maqy0827/22GD/Book/Image/PCB-已焊接.jpg

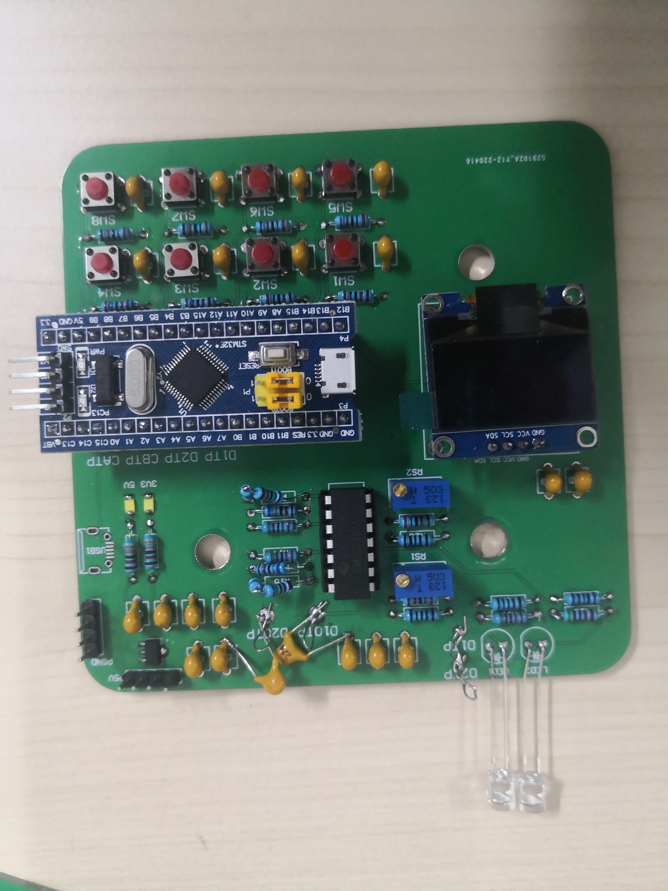
Book/Image/PCB-已焊接.jpg
