maqy0827/22GD/Book/Image/PCB-未焊接.jpg

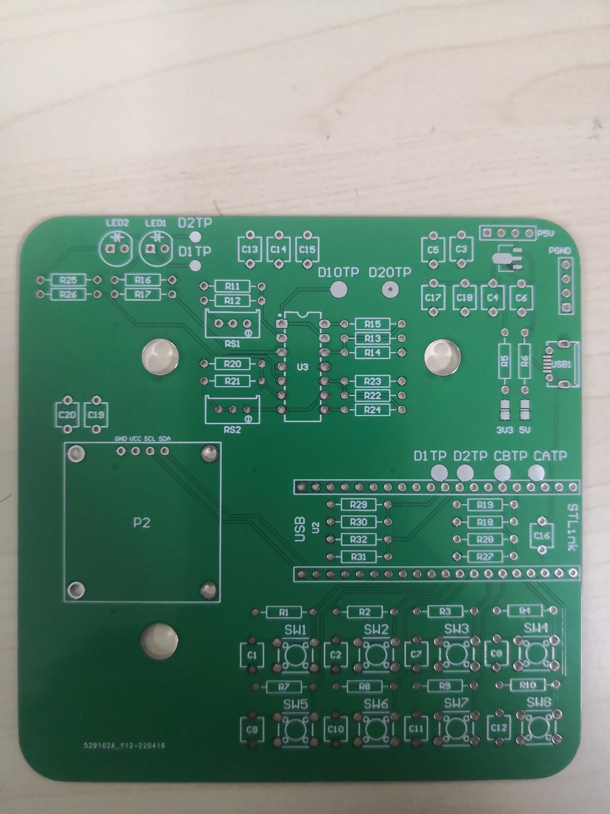
Book/Image/PCB-未焊接.jpg
