maqy0827/22GD/Book/Image/分光片干涉图样.jpg

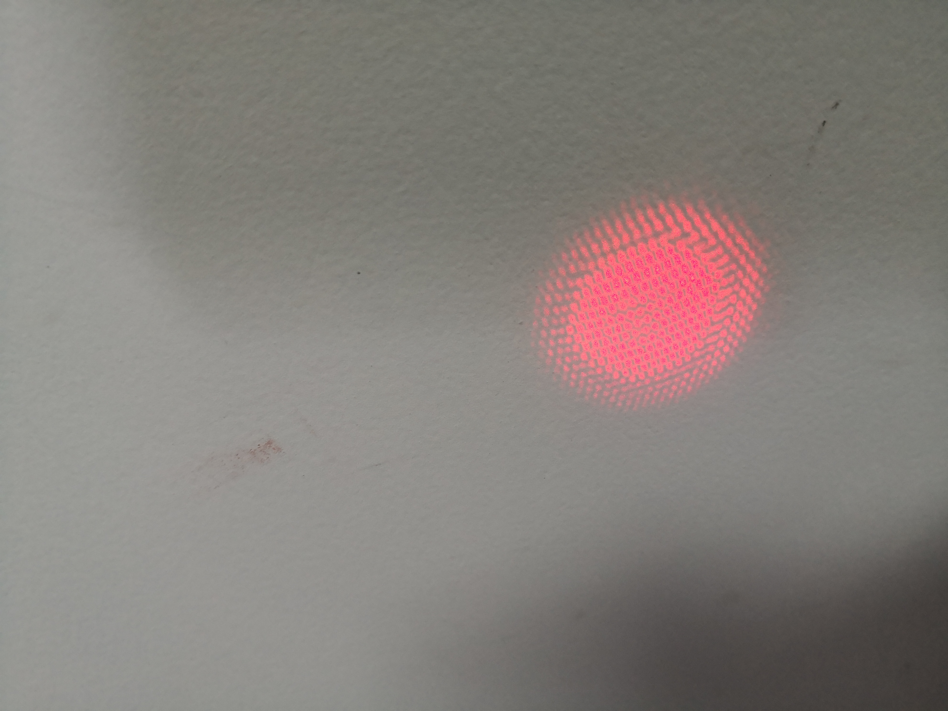
Book/Image/分光片干涉图样.jpg
