maqy0827/22GD/Book/Image/并联101原始信号.jpg

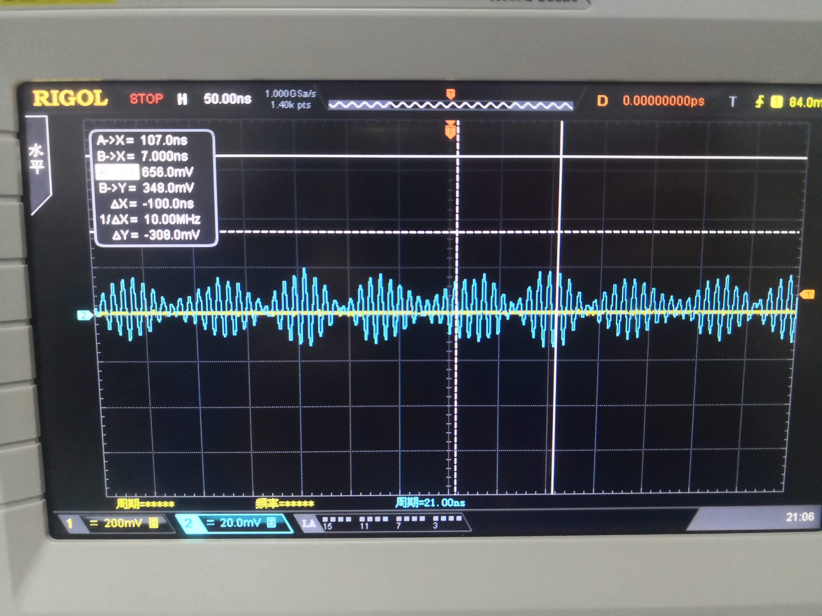
Book/Image/并联101原始信号.jpg
