maqy0827/22GD/Book/Image/放大前.jpg

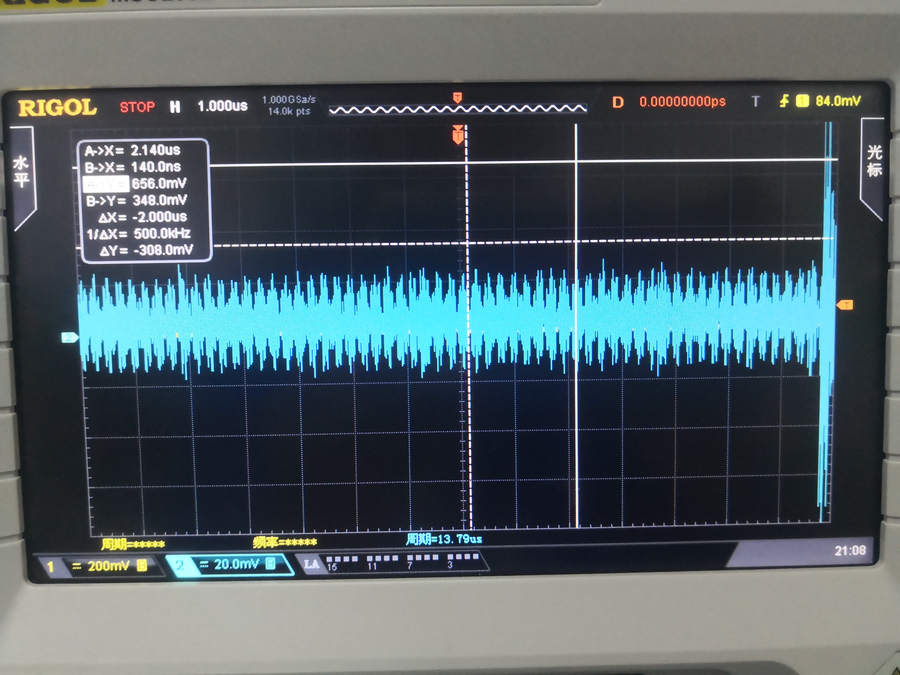
Book/Image/放大前.jpg
