maqy0827/22GD/Book/Image/放大后无滤波暗光.jpg

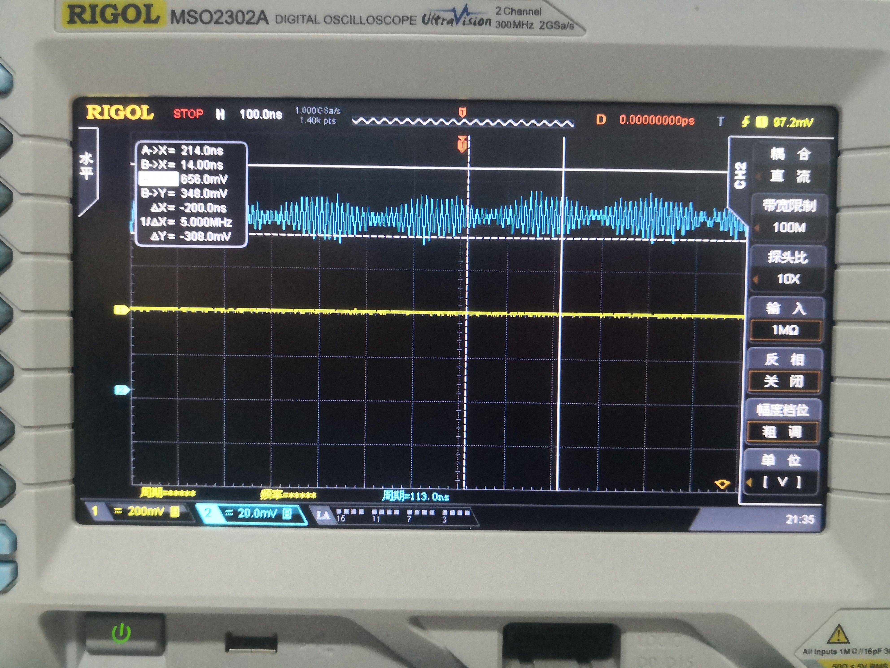
Book/Image/放大后无滤波暗光.jpg
