maqy0827/22GD/Book/Image/数据处理.png

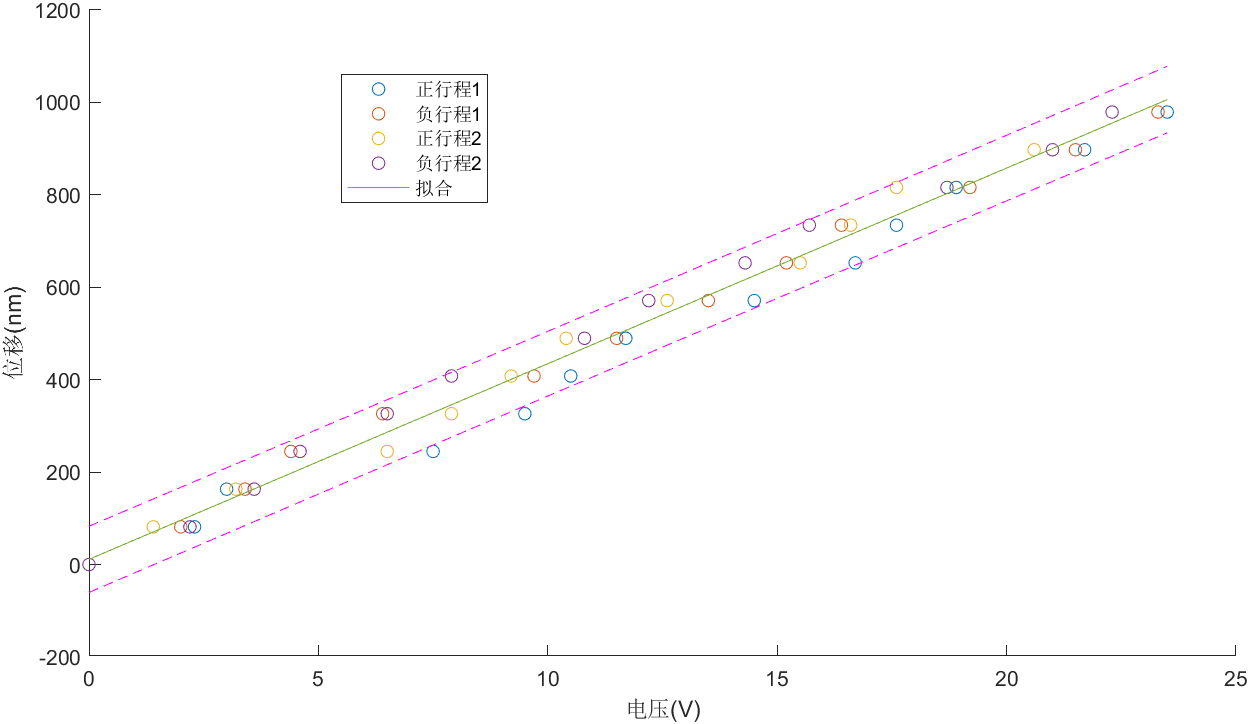
Book/Image/数据处理.png
