maqy0827/22GD/Book/Image/环境光-未滤波.jpg

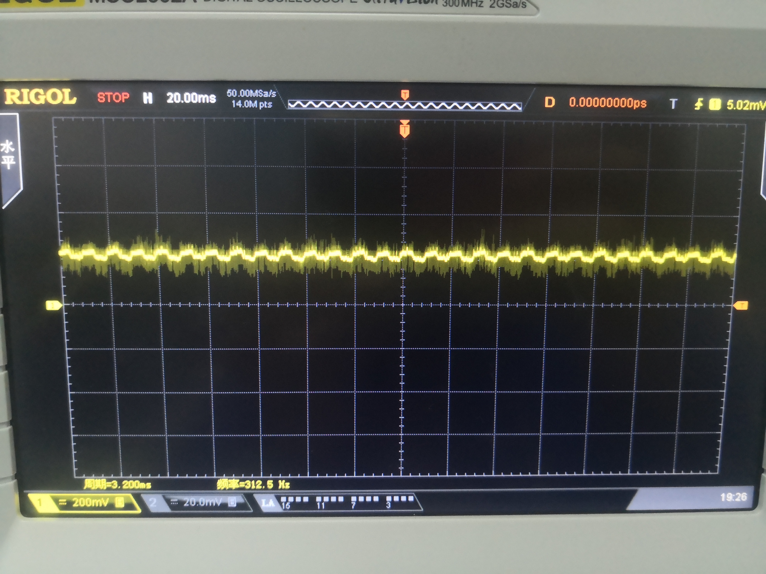
Book/Image/环境光-未滤波.jpg
